Architeuthis-Flux/IGV1-16_Driver_Backpack/Hardware/IGV1.png

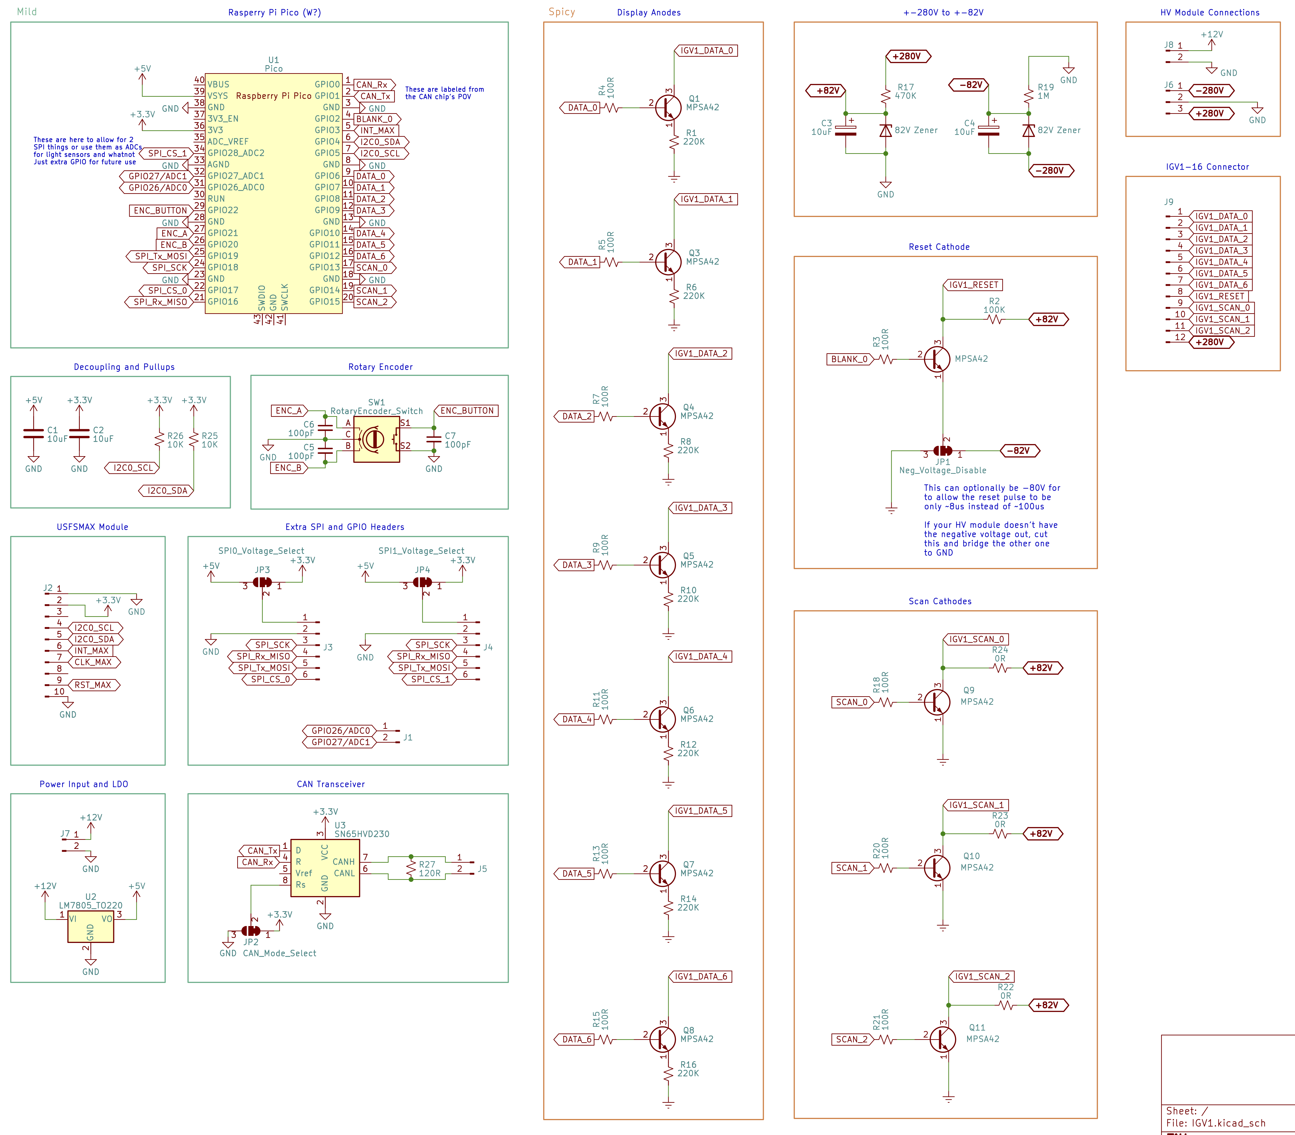
Hardware/IGV1.png
