Architeuthis-Flux/IGV1-16_Driver_Backpack/Hardware/igvback.png

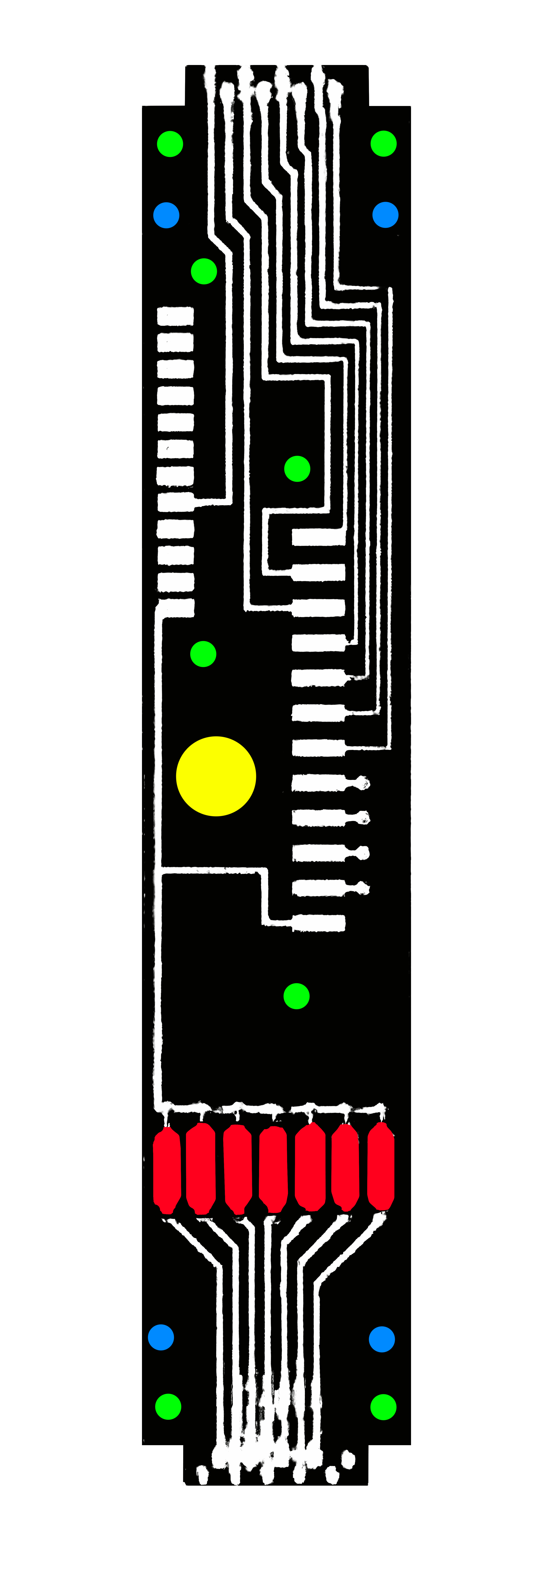
Hardware/igvback.png
