Architeuthis-Flux/IGV1-16_Driver_Backpack/Hardware/Screenshot 2023-03-13 at 5.15.55 PM.jpeg

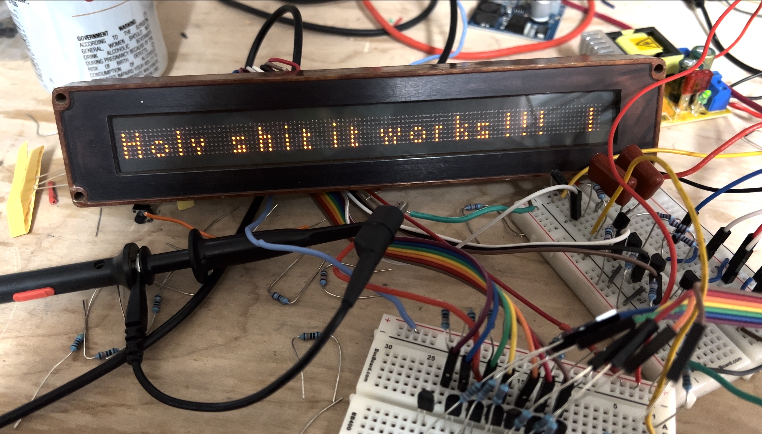
Hardware/Screenshot 2023-03-13 at 5.15.55 PM.jpeg
