Architeuthis-Flux/IGV1-16_Driver_Backpack/Hardware/Screenshot 2023-03-19 at 2.11.21 PM.png

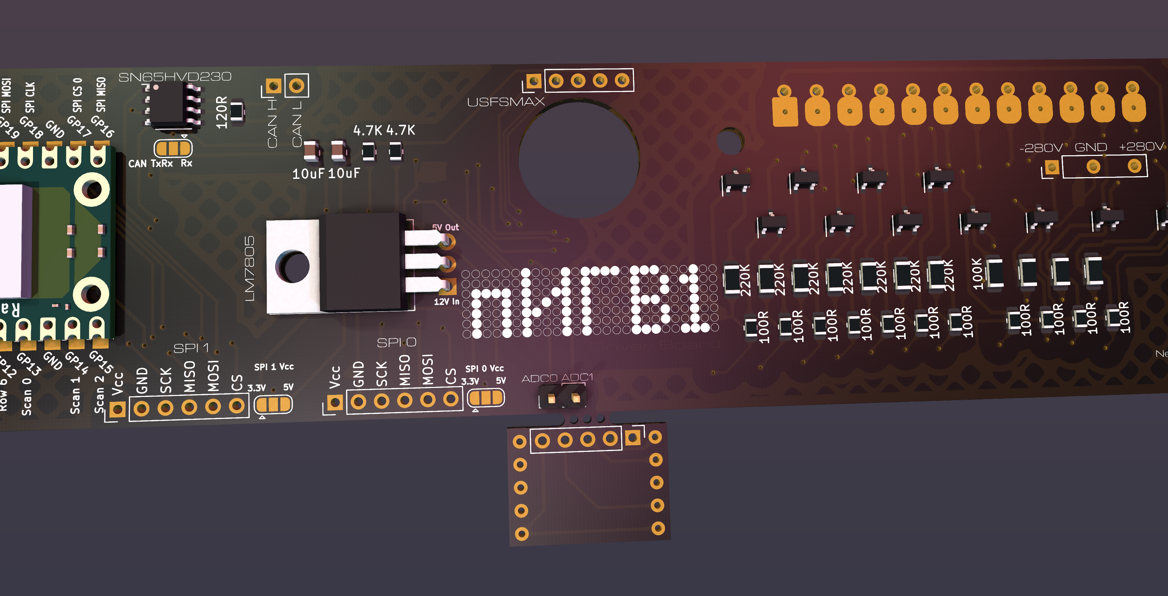
Hardware/Screenshot 2023-03-19 at 2.11.21 PM.png
