Architeuthis-Flux/IGV1-16_Driver_Backpack/Hardware/Screenshot 2023-03-19 at 2.12.13 PM.png

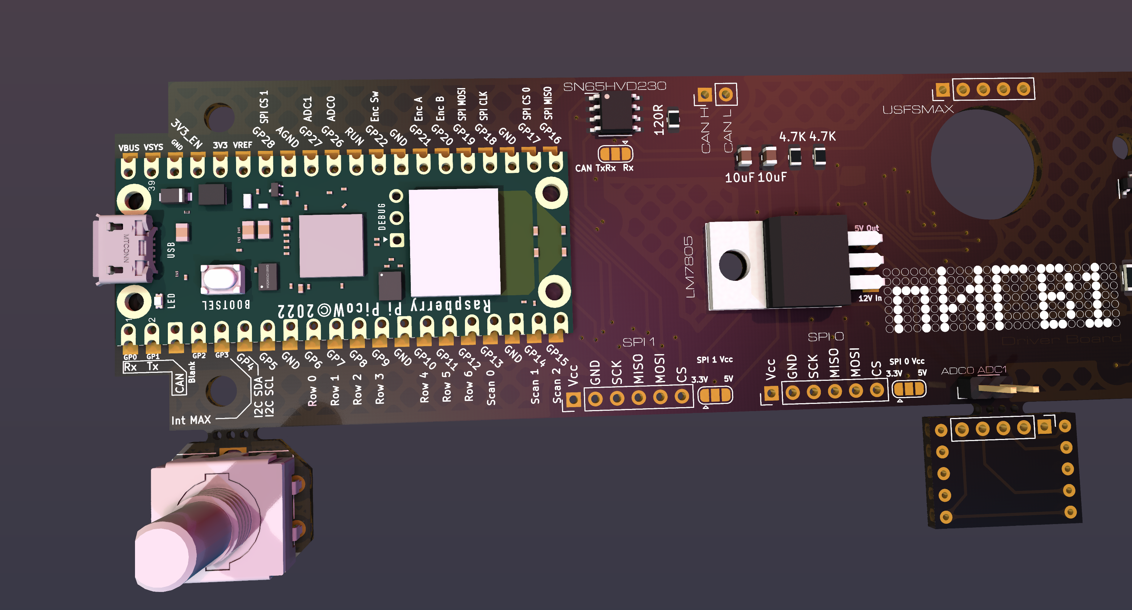
Hardware/Screenshot 2023-03-19 at 2.12.13 PM.png
