Architeuthis-Flux/IGV1-16_Driver_Backpack/Hardware/IGV1_KicadFiles/IGV1.kicad_sch

## KiCad design Hardware/IGV1_KicadFiles/IGV1.kicad_sch (2024-07-26)

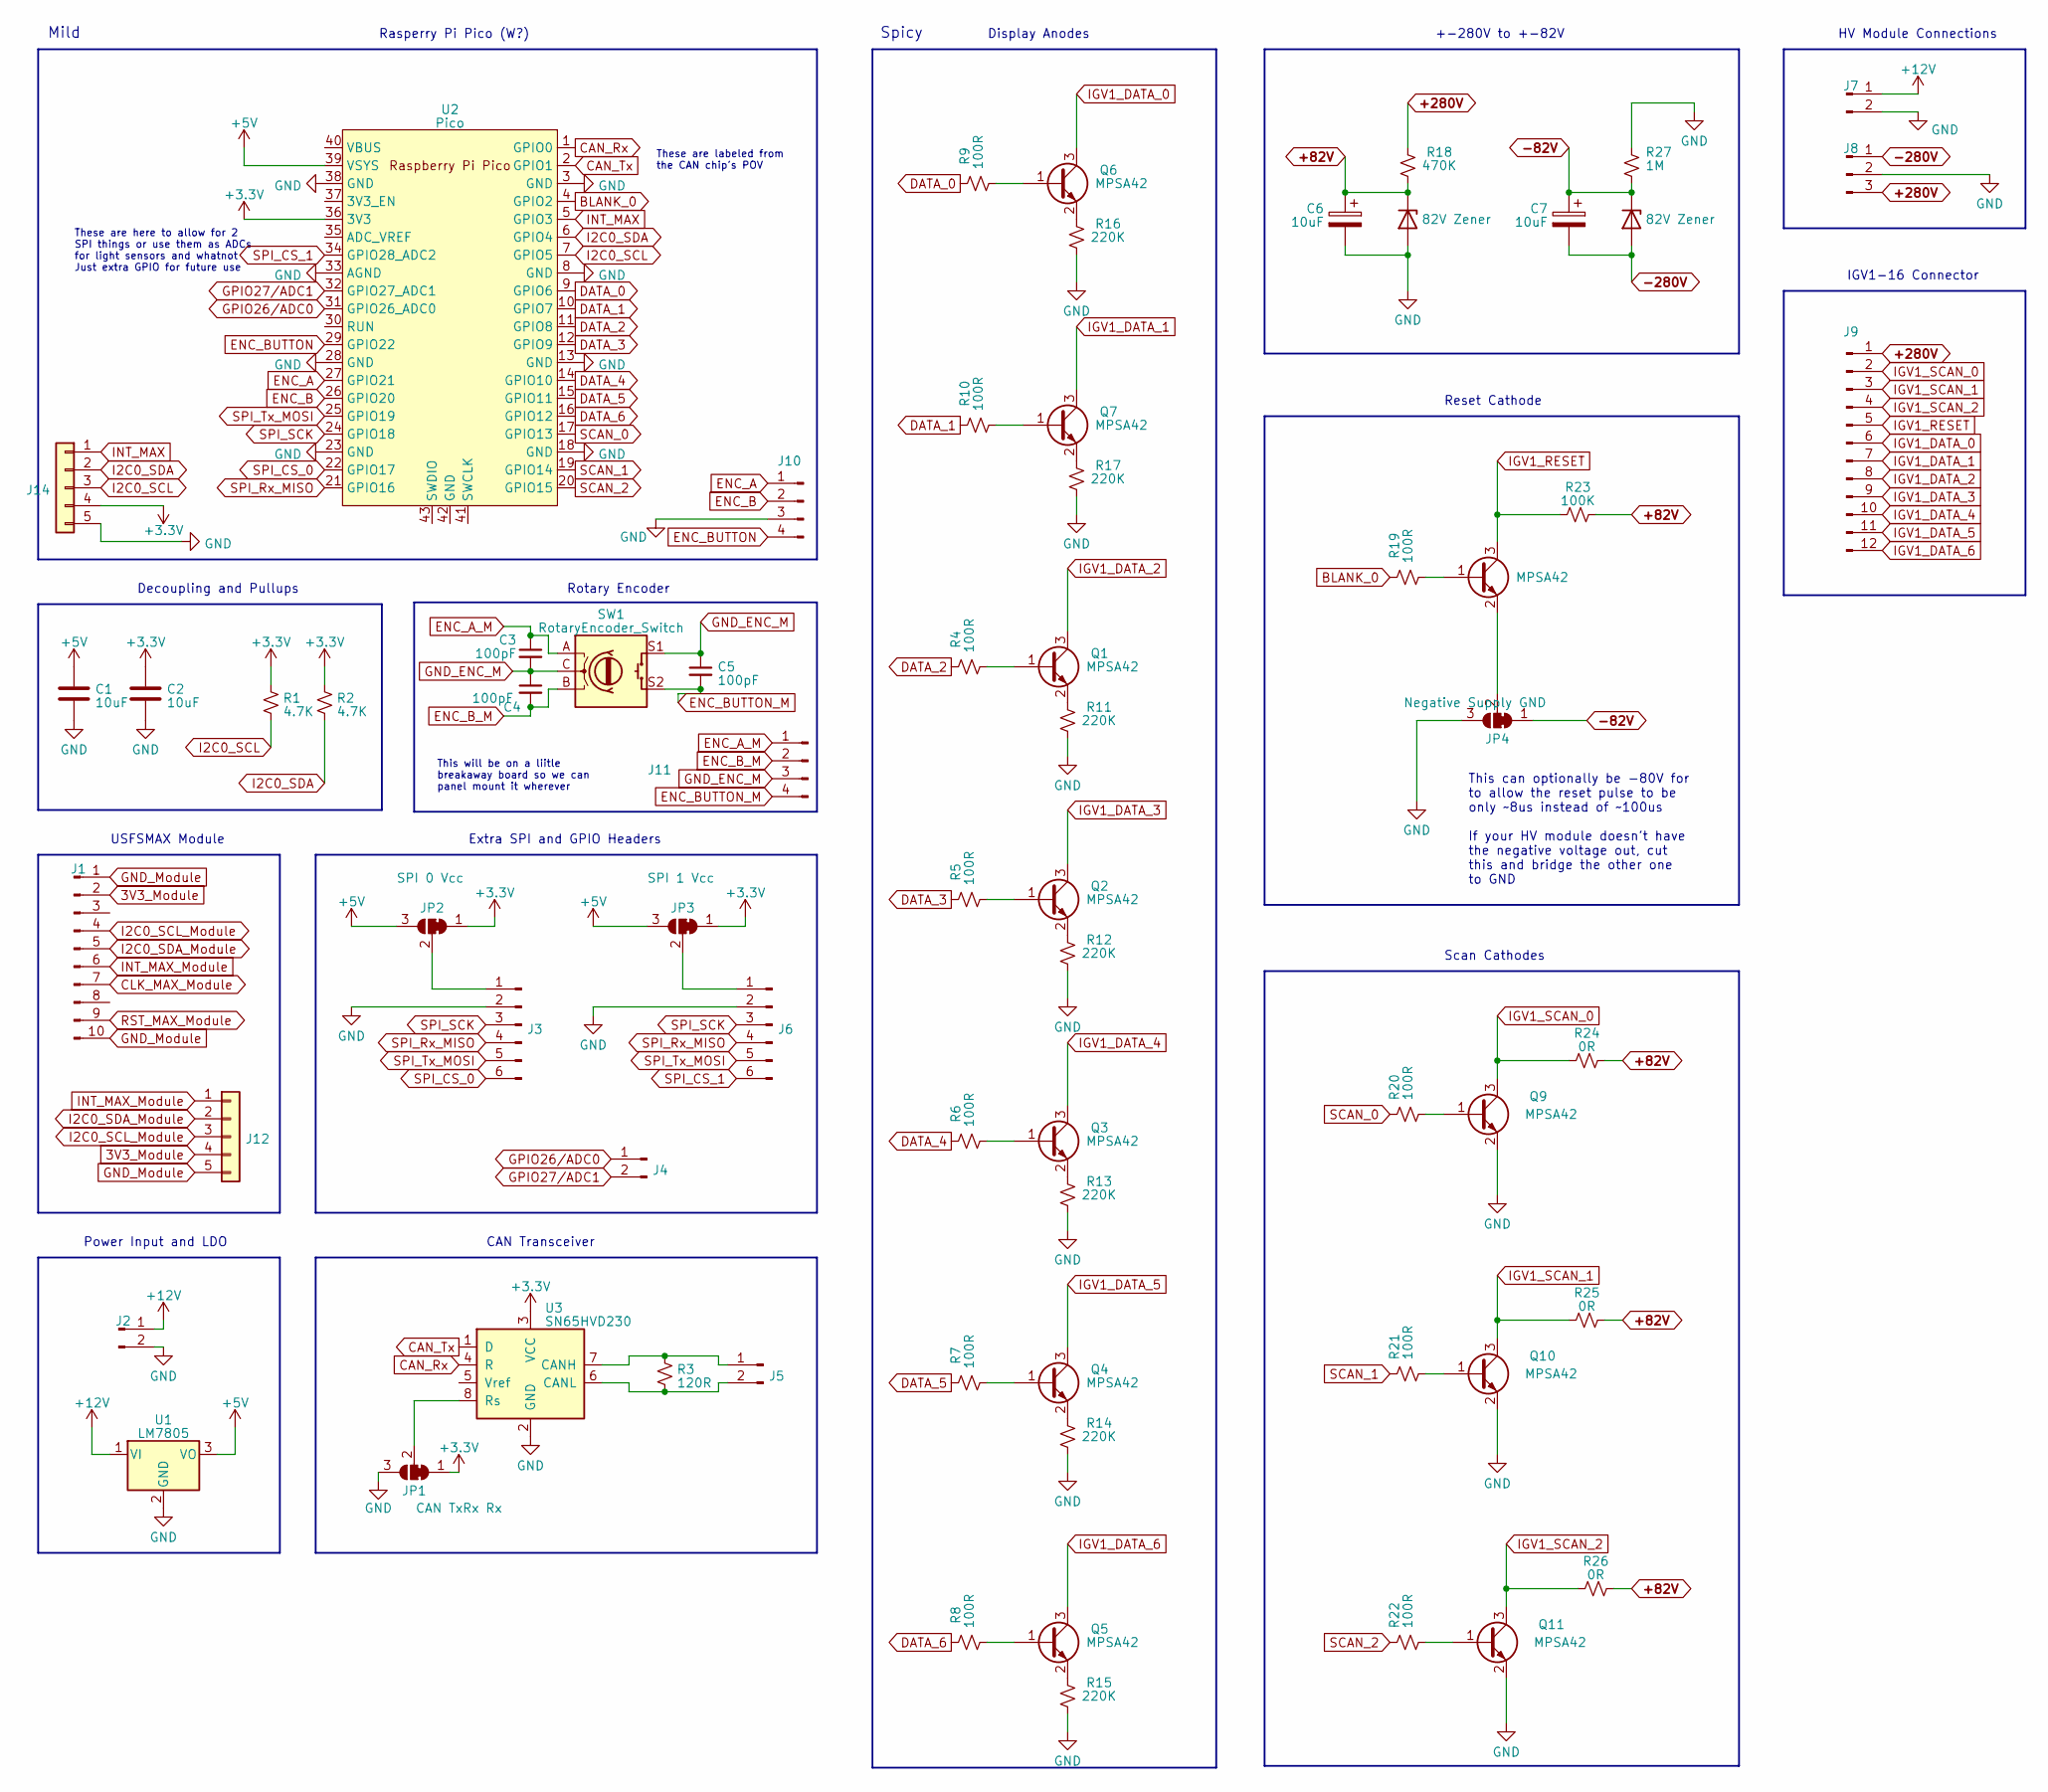
[picture p20: schematic IGV1.kicad_sch]

Parts:
C1, C2: 10uF; C_0805_2012Metric_Pad1.18x1.45mm_HandSolder
C3, C4, C5: 100pF; C_0805_2012Metric_Pad1.18x1.45mm_HandSolder
C6, C7: 10uF; C_Radial_D6.3mm_H11.0mm_P2.50mm
D1, D2: 82V Zener; D_A-405_P7.62mm_Horizontal
J1: Conn_01x10_Pin; USFSMAX
J2: GND 12V; PinHeader_1x02_P2.54mm_Vertical
J3: SPI 0; PinHeader_1x06_P2.54mm_Vertical_SPI
J4: ADC0 ADC1; PinHeader_1x02_P2.54mm_Vertical
J5: CAN_H CAN_L; PinHeader_1x02_P2.54mm_Vertical
J6: SPI 1; PinHeader_1x06_P2.54mm_Vertical_SPI
J7: GND 12V; PinHeader_1x03_P2.54mm_Vertical
J8: -280V GND +280V; PinHeader_1x06_P2.54mm_Vertical
J9: Conn_01x12_Pin; PinHeader_1x12_P2.54mm_Vertical
J10, J11: Conn_01x04_Pin; PinHeader_2x02_P2.54mm_Vertical
J12: Conn_01x05; PinHeader_1x05_P2.54mm_Vertical
J14: USFSMAX; PinHeader_1x05_P2.54mm_Vertical
JP1: CAN TxRx Rx; SolderJumper-3_P1.3mm_Bridged12_RoundedPad1.0x1.5mm
JP2: SPI 0 Vcc; SolderJumper-3_P1.3mm_Bridged12_RoundedPad1.0x1.5mm
JP3: SPI 1 Vcc; SolderJumper-3_P1.3mm_Bridged12_RoundedPad1.0x1.5mm
JP4: Negative Supply GND; SolderJumper-3_P1.3mm_Bridged12_RoundedPad1.0x1.5mm
Q1, Q2, Q3, Q4, Q5, Q6, Q7, Q8, Q9, Q10, Q11: MPSA42; SOT-23
R1, R2: 4.7K; R_0805_2012Metric_Pad1.20x1.40mm_HandSolder
R3: 120R; R_0805_2012Metric_Pad1.20x1.40mm_HandSolder
R4, R5, R6, R7, R8, R9, R10, R19, R20, R21, R22: 100R; R_0805_2012Metric_Pad1.20x1.40mm_HandSolder
R11, R12, R13, R14, R15, R16, R17: 220K; R_1206_3216Metric_Pad1.30x1.75mm_HandSolder
R18: 470K; R_1206_3216Metric_Pad1.30x1.75mm_HandSolder
R23: 100K; R_1206_3216Metric_Pad1.30x1.75mm_HandSolder
R24, R25, R26: 0R; R_1206_3216Metric_Pad1.30x1.75mm_HandSolder
R27: 1M; R_1206_3216Metric_Pad1.30x1.75mm_HandSolder
SW1: RotaryEncoder_Switch; RotaryEncoder_Alps_EC12E-Switch_Vertical_H20mm
U1: LM7805; TO-220-3_Horizontal_TabDown
U2: Pico; RPi_Pico_SMD_TH_1
U3: SN65HVD230; SOIC-8_3.9x4.9mm_P1.27mm

Connections:
3V3_Module: J1.2, J12.4
+3.3V: C2.1, J14.4, JP1.1 (A), JP2.1 (A), JP3.1 (A), R1.1, R2.1, U2.36 (3V3), U3.3 (VCC)
+5V: C1.1, JP2.3 (B), JP3.3 (B), U1.3 (VO), U2.39 (VSYS)
+12V: J2.1, J7.1, U1.1 (VI)
+82V: C6.1, D1.1 (K), R18.2, R23.2, R24.2, R25.2, R26.2
+280V: J8.3, J9.1, R18.1
-82V: C7.1, D2.1 (K), JP4.1 (A), R27.2
-280V: C7.2, D2.2 (A), J8.1
BLANK_0: R19.1, U2.4 (GPIO2)
CAN_Rx: U2.1 (GPIO0), U3.4 (R)
CAN_Tx: U2.2 (GPIO1), U3.1 (D)
CLK_MAX_Module: J1.7
DATA_0: R9.1, U2.9 (GPIO6)
DATA_1: R10.1, U2.10 (GPIO7)
DATA_2: R4.1, U2.11 (GPIO8)
DATA_3: R5.1, U2.12 (GPIO9)
DATA_4: R6.1, U2.14 (GPIO10)
DATA_5: R7.1, U2.15 (GPIO11)
DATA_6: R8.1, U2.16 (GPIO12)
ENC_A: J10.1, U2.27 (GPIO21)
ENC_A_M: C3.1, J11.1, SW1.A
ENC_B: J10.2, U2.26 (GPIO20)
ENC_BUTTON: J10.4, U2.29 (GPIO22)
ENC_BUTTON_M: C5.2, J11.4, SW1.S2
ENC_B_M: C4.2, J11.2, SW1.B
GND: C1.2, C2.2, C6.2, D1.2 (A), J2.2, J3.2, J6.2, J7.2, J8.2, J10.3, J14.5, JP1.3 (B), JP4.3 (B), Q9.2 (E), Q10.2 (E), Q11.2 (E), R11.2, R12.2, R13.2, R14.2, R15.2, R16.2, R17.2, R27.1, U1.2 (GND), U2.3 (GND), U2.8 (GND), U2.13 (GND), U2.18 (GND), U2.23 (GND), U2.28 (GND), U2.33 (AGND), U2.38 (GND), U3.2 (GND)
GND_ENC_M: C3.2, C4.1, C5.1, J11.3, SW1.C, SW1.S1
GND_Module: J1.1, J1.10, J12.5
GPIO26/ADC0: J4.1, U2.31 (GPIO26_ADC0)
GPIO27/ADC1: J4.2, U2.32 (GPIO27_ADC1)
I2C0_SCL: J14.3, R1.2, U2.7 (GPIO5)
I2C0_SCL_Module: J1.4, J12.3
I2C0_SDA: J14.2, R2.2, U2.6 (GPIO4)
I2C0_SDA_Module: J1.5, J12.2
IGV1_DATA_0: J9.6, Q6.3 (C)
IGV1_DATA_1: J9.7, Q7.3 (C)
IGV1_DATA_2: J9.8, Q1.3 (C)
IGV1_DATA_3: J9.9, Q2.3 (C)
IGV1_DATA_4: J9.10, Q3.3 (C)
IGV1_DATA_5: J9.11, Q4.3 (C)
IGV1_DATA_6: J9.12, Q5.3 (C)
IGV1_RESET: J9.5, Q8.3 (C), R23.1
IGV1_SCAN_0: J9.2, Q9.3 (C), R24.1
IGV1_SCAN_1: J9.3, Q10.3 (C), R25.1
IGV1_SCAN_2: J9.4, Q11.3 (C), R26.1
INT_MAX: J14.1, U2.5 (GPIO3)
INT_MAX_Module: J1.6, J12.1
unnamed: J3.1, JP2.2 (C)
unnamed: J5.1, R3.1, U3.7 (CANH)
unnamed: J5.2, R3.2, U3.6 (CANL)
unnamed: J6.1, JP3.2 (C)
unnamed: JP1.2 (C), U3.8 (Rs)
unnamed: JP4.2 (C), Q8.2 (E)
unnamed: Q1.1 (B), R4.2
unnamed: Q1.2 (E), R11.1
unnamed: Q2.1 (B), R5.2
unnamed: Q2.2 (E), R12.1
unnamed: Q3.1 (B), R6.2
unnamed: Q3.2 (E), R13.1
unnamed: Q4.1 (B), R7.2
unnamed: Q4.2 (E), R14.1
unnamed: Q5.1 (B), R8.2
unnamed: Q5.2 (E), R15.1
unnamed: Q6.1 (B), R9.2
unnamed: Q6.2 (E), R16.1
unnamed: Q7.1 (B), R10.2
unnamed: Q7.2 (E), R17.1
unnamed: Q8.1 (B), R19.2
unnamed: Q9.1 (B), R20.2
unnamed: Q10.1 (B), R21.2
unnamed: Q11.1 (B), R22.2
RST_MAX_Module: J1.9
SCAN_0: R20.1, U2.17 (GPIO13)
SCAN_1: R21.1, U2.19 (GPIO14)
SCAN_2: R22.1, U2.20 (GPIO15)
SPI_CS_0: J3.6, U2.22 (GPIO17)
SPI_CS_1: J6.6, U2.34 (GPIO28_ADC2)
SPI_Rx_MISO: J3.4, J6.4, U2.21 (GPIO16)
SPI_SCK: J3.3, J6.3, U2.24 (GPIO18)
SPI_Tx_MOSI: J3.5, J6.5, U2.25 (GPIO19)

Notes on the sheet:
Rasperry Pi Pico (W?)
CAN Transceiver
Spicy
Display Anodes
Rotary Encoder
These are labeled from the CAN chip's POV
IGV1-16 Connector
This will be on a liitle breakaway board so we can panel mount it wherever
Decoupling and Pullups
Reset Cathode
Power Input and LDO
HV Module Connections
Mild
Extra SPI and GPIO Headers
USFSMAX Module
+-280V to +-82V
This can optionally be -80V for to allow the reset pulse to be only ~8us instead of ~100us If your HV module doesn't have the negative voltage out, cut this and bridge the other one to GND
Scan Cathodes
These are here to allow for 2 SPI things or use them as ADCs for light sensors and whatnot Just extra GPIO for future use
