Architeuthis-Flux/IGV1-16_Driver_Backpack/Code/PIGV_USFS_Compass/src/bitmaps.h

unsigned char compass[]{
  0x78, 0x7c, 0x7e, 0x7e, 0x7f, 0x7f, 0x7f, 0x7f, 0x7f, 0x7e, 0x7e, 0x7e, 0x7e, 0x7e, 0x7f, 0x7f,
  0x7f, 0x7f, 0x7f, 0x7e, 0x7e, 0x7e, 0x7e, 0x7f, 0x7f, 0x7f, 0x7f, 0x7e, 0x7e, 0x7e, 0x7f, 0x7f,
  0x7f, 0x7e, 0x7e, 0x7f, 0x7f, 0x7e, 0x7e, 0x6e, 0x6e, 0x7e, 0x7f, 0x03, 0x3f, 0x5e, 0x3f, 0x03,
  0x7f, 0x7e, 0x6e, 0x6e, 0x7e, 0x7e, 0x7f, 0x7f, 0x7e, 0x7e, 0x7f, 0x7f, 0x7f, 0x7e, 0x7e, 0x7e,
  0x7f, 0x7f, 0x7f, 0x7f, 0x7e, 0x7e, 0x7e, 0x7e, 0x7f, 0x7f, 0x7f, 0x7f, 0x7f, 0x7e, 0x7e, 0x7e,
  0x7e, 0x7e, 0x7f, 0x7f, 0x7f, 0x7f, 0x7f, 0x7e, 0x7e, 0x7c, 0x78, 0x7c, 0x7e, 0x7e, 0x7f, 0x7f,
  0x7f, 0x7f, 0x7f, 0x7e, 0x7e, 0x7e, 0x7e, 0x7e, 0x7f, 0x7f, 0x7f, 0x7f, 0x7f, 0x7e, 0x7e, 0x7e,
  0x7e, 0x7f, 0x7f, 0x7f, 0x7f, 0x7e, 0x7e, 0x7e, 0x7f, 0x7f, 0x7f, 0x7e, 0x7e, 0x7f, 0x7f, 0x7e,
  0x7e, 0x6e, 0x6e, 0x7e, 0x7f, 0x03, 0x77, 0x6e, 0x5f, 0x03, 0x7f, 0x7e, 0x6e, 0x6e, 0x7e, 0x7e,
  0x7f, 0x7f, 0x7e, 0x7e, 0x7f, 0x7f, 0x7f, 0x7e, 0x7e, 0x7e, 0x7f, 0x7f, 0x7f, 0x7f, 0x7e, 0x7e,
  0x7e, 0x7e, 0x7f, 0x7f, 0x7f, 0x7f, 0x7f, 0x7e, 0x7e, 0x7e, 0x7e, 0x7e, 0x7f, 0x7f, 0x7f, 0x7f,
  0x7f, 0x7e, 0x7e, 0x7c, 0x78, 0x7c, 0x7e, 0x7e, 0x7f, 0x7f, 0x7f, 0x7f, 0x7f, 0x7e, 0x7e, 0x7e,
  0x7e, 0x7e, 0x7f, 0x7f, 0x7f, 0x7f, 0x7f, 0x7e, 0x7e, 0x7e, 0x7e, 0x7f, 0x7f, 0x7f, 0x7f, 0x7e,
  0x7e, 0x7e, 0x7f, 0x7f, 0x7f, 0x7e, 0x7e, 0x7f, 0x7f, 0x7e, 0x7e, 0x6e, 0x6e, 0x7e, 0x7f, 0x03,
  0x2b, 0x2a, 0x2b, 0x3b, 0x7f, 0x7e, 0x6e, 0x6e, 0x7e, 0x7e, 0x7f, 0x7f, 0x7e, 0x7e, 0x7f, 0x7f,
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
	0b10011011, //  ##  #  
	0b10101011, //  # # #  
	0b10110011, //  #  ##  
	0b10111011 //  #   #  
	},{
	0b11111111, //         
	0b11110111, //     #   
	0b11001001, //   ## ## 
	0b10111110, //  #     #
	0b11111111 //         
	},{
	0b11111111, //         
	0b11111111, //         
	0b10000000, //  #######
	0b11111111, //         
	0b11111111 //         
	},{
	0b11111111, //         
	0b10111110, //  #     #
	0b11001001, //   ## ## 
	0b11110111, //     #   
	0b11111111} //         
};
